StanfordMSL/ouijabot/Hardware/CAD/motor-mount-pololu-1995.SLDPRT

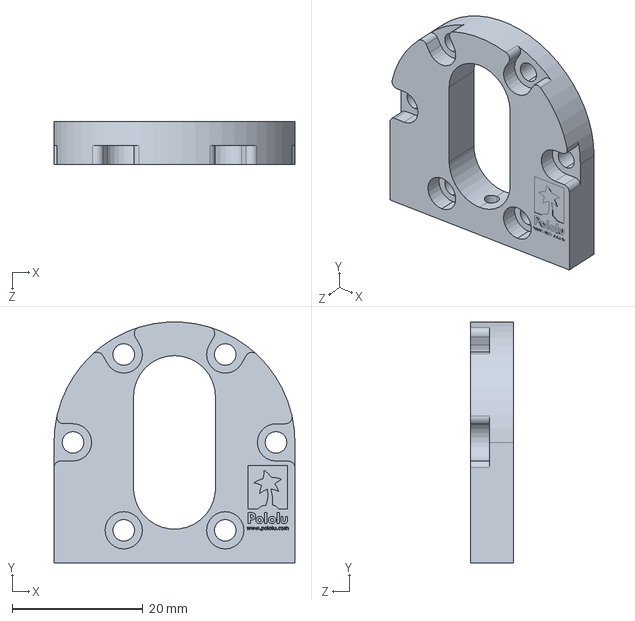
[picture p15: CAD file, 2019-09-23]
Hardware/CAD/motor-mount-pololu-1995.SLDPRT
36.8 x 36.8 x 6.50 mm
