StanfordMSL/ouijabot/Hardware/CAD/level2-plate.SLDPRT

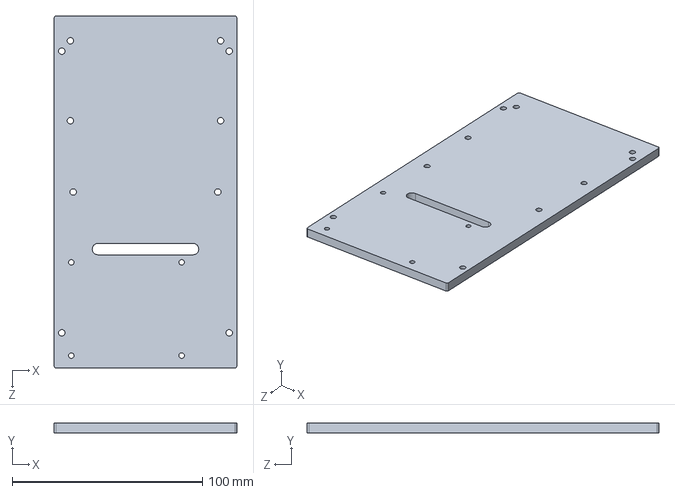
[picture p16: CAD file, 2019-09-23]
Hardware/CAD/level2-plate.SLDPRT
96.0 x 5.00 x 185.0 mm
