StanfordMSL/ouijabot/Hardware/electronics/ouijabot.sch

## EAGLE design Hardware/electronics/ouijabot.sch (2019-09-23)

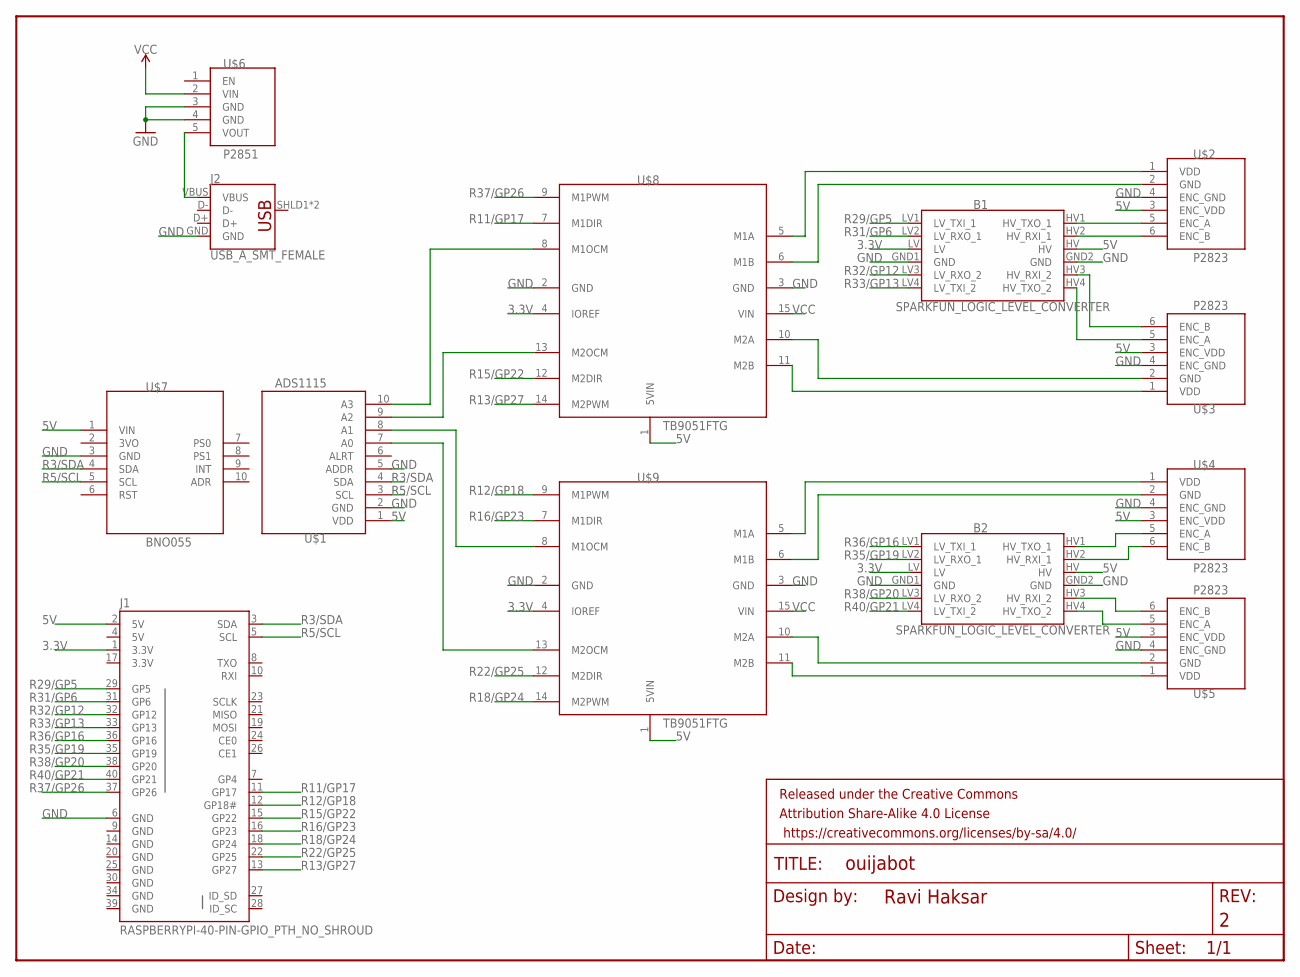
[picture p18: schematic ouijabot.sch]

Parts:
B1, B2: SPARKFUN_LOGIC_LEVEL_CONVERTER
FRAME1: FRAME-LETTER; CREATIVE_COMMONS
J1: RASPBERRYPI-40-PIN-GPIO_PTH_NO_SHROUD; 2X20
J2: USB_A_SMT_FEMALE; USB-A-S-SILK-FEMALE
U$1: ADS1115; 10X10MTA
U$2, U$3, U$4, U$5: P2823; 1X06
U$6: P2851; 1X05
U$7: BNO055; 1X10
U$8, U$9: TB9051FTG; 1X15

Connections:
3.3V: B1.LV, B2.LV, J1.1 (3.3V), U$8.4 (IOREF), U$9.4 (IOREF)
5V: B1.HV, B2.HV, J1.2 (5V), U$1.1 (VDD), U$2.3 (ENC_VDD), U$3.3 (ENC_VDD), U$4.3 (ENC_VDD), U$5.3 (ENC_VDD), U$7.1 (VIN), U$8.1 (5VIN), U$9.1 (5VIN)
GND: B1.GND1 (GND), B1.GND2 (GND), B2.GND1 (GND), B2.GND2 (GND), J1.6 (GND), J2.GND, U$1.2 (GND), U$1.5 (ADDR), U$2.4 (ENC_GND), U$3.4 (ENC_GND), U$4.4 (ENC_GND), U$5.4 (ENC_GND), U$6.3 (GND), U$6.4 (GND), U$7.3 (GND), U$8.2 (GND), U$8.3 (GND), U$9.2 (GND), U$9.3 (GND)
unnamed: J2.VBUS, U$6.5 (VOUT)
unnamed: U$2.1 (VDD), U$8.5 (M1A)
unnamed: U$2.2 (GND), U$8.6 (M1B)
unnamed: B1.HV4 (HV_TXO_2), U$3.5 (ENC_A)
unnamed: U$3.2 (GND), U$8.10 (M2A)
unnamed: B1.HV1 (HV_TXO_1), U$2.5 (ENC_A)
unnamed: B1.HV2 (HV_RXI_1), U$2.6 (ENC_B)
unnamed: B1.HV3 (HV_RXI_2), U$3.6 (ENC_B)
unnamed: U$3.1 (VDD), U$8.11 (M2B)
unnamed: U$4.1 (VDD), U$9.5 (M1A)
unnamed: U$4.2 (GND), U$9.6 (M1B)
unnamed: B2.HV2 (HV_RXI_1), U$4.6 (ENC_B)
unnamed: B2.HV1 (HV_TXO_1), U$4.5 (ENC_A)
unnamed: B2.HV3 (HV_RXI_2), U$5.6 (ENC_B)
unnamed: B2.HV4 (HV_TXO_2), U$5.5 (ENC_A)
unnamed: U$5.2 (GND), U$9.10 (M2A)
unnamed: U$5.1 (VDD), U$9.11 (M2B)
unnamed: U$1.10 (A3), U$8.8 (M1OCM)
unnamed: U$1.9 (A2), U$8.13 (M2OCM)
unnamed: U$1.8 (A1), U$9.8 (M1OCM)
unnamed: U$1.7 (A0), U$9.13 (M2OCM)
R3/SDA: J1.3 (SDA), U$1.4 (SDA), U$7.4 (SDA)
R5/SCL: J1.5 (SCL), U$1.3 (SCL), U$7.5 (SCL)
R11/GP17: J1.11 (GP17), U$8.7 (M1DIR)
R12/GP18: J1.12 (GP18#), U$9.9 (M1PWM)
R13/GP27: J1.13 (GP27), U$8.14 (M2PWM)
R15/GP22: J1.15 (GP22), U$8.12 (M2DIR)
R16/GP23: J1.16 (GP23), U$9.7 (M1DIR)
R18/GP24: J1.18 (GP24), U$9.14 (M2PWM)
R22/GP25: J1.22 (GP25), U$9.12 (M2DIR)
R29/GP5: B1.LV1 (LV_TXI_1), J1.29 (GP5)
R31/GP6: B1.LV2 (LV_RXO_1), J1.31 (GP6)
R32/GP12: B1.LV3 (LV_RXO_2), J1.32 (GP12)
R33/GP13: B1.LV4 (LV_TXI_2), J1.33 (GP13)
R35/GP19: B2.LV2 (LV_RXO_1), J1.35 (GP19)
R36/GP16: B2.LV1 (LV_TXI_1), J1.36 (GP16)
R37/GP26: J1.37 (GP26), U$8.9 (M1PWM)
R38/GP20: B2.LV3 (LV_RXO_2), J1.38 (GP20)
R40/GP21: B2.LV4 (LV_TXI_2), J1.40 (GP21)
VCC: U$6.2 (VIN), U$8.15 (VIN), U$9.15 (VIN)
